bernd2704-cpu/bTn_Wecker/Hardware/Schaltplan/KiCad_Wecker_2v0/Wecker_2v0.kicad_sch

## KiCad design Hardware/Schaltplan/KiCad_Wecker_2v0/Wecker_2v0.kicad_sch (2026-10-06)

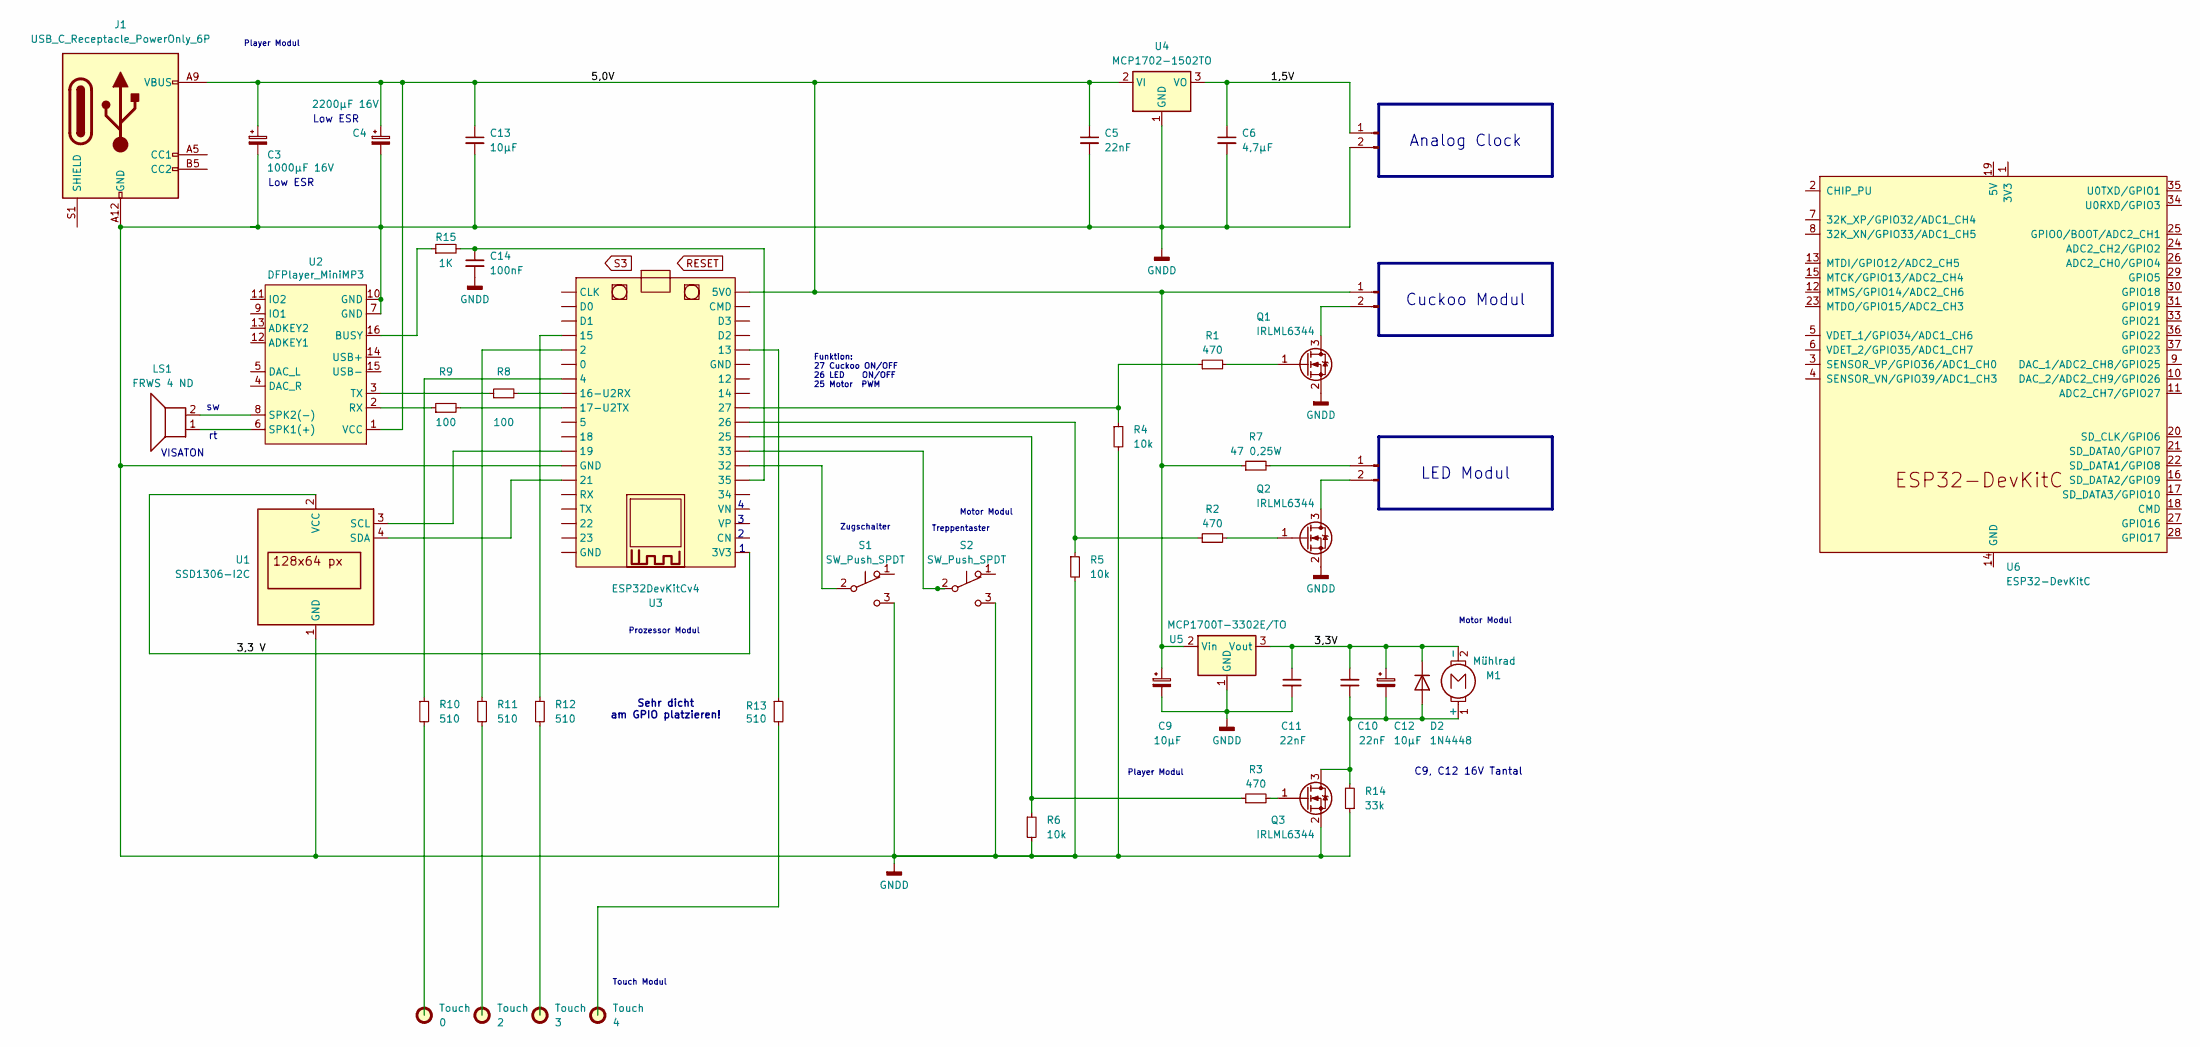
[picture p9: schematic Wecker_2v0.kicad_sch]

Parts:
C3: 1000µF 16V
C4: 2200µF 16V
C5, C10, C11: 22nF
C6: 4,7µF
C9, C12, C13: 10µF
C14: 100nF
D2: 1N4448; D_DO-41_SOD81_P10.16mm_Horizontal
J1: USB_C_Receptacle_PowerOnly_6P
J2, J3, J4: Conn_01x02_Pin
LS1: FRWS 4 ND
M1: Mühlrad
Q1, Q2, Q3: IRLML6344; SOT-23
R1, R2, R3: 470
R4, R5, R6: 10k
R7: 47 0,25W
R8, R9: 100
R10, R11, R12, R13: 510
R14: 33k
R15: 1K
S1, S2: SW_Push_SPDT
Touch: 4
U1: SSD1306-I2C; 0.96" SSD1306
U2: DFPlayer_MiniMP3
U3: ESP32DevKitCv4
U4: MCP1702-1502TO; SOT-223-3_TabPin2
U5: MCP1700T-3302E/TO; SOT-223-3_TabPin2
U6: ESP32-DevKitC

Connections:
1,5V: C6.1, J2.1, U4.3 (VO)
3,3 V: U1.2 (VCC), U3.20 (3V3)
3,3V: C10.1, C11.1, C12.1, D2.1 (K), M1.2 (-), U5.3 (Vout)
5,0V: C3.1, C4.1, C5.1, C9.1, C13.1, J1.A9 (VBUS), J1.B9 (VBUS), J3.1, R7.1, U2.1 (VCC), U3.38 (5V0), U4.2 (VI), U5.2 (Vin)
GNDD: C3.2, C4.2, C5.2, C6.2, C9.2, C11.2, C13.2, C14.2, J1.A12 (GND), J1.B12 (GND), J2.2, Q1.2 (S), Q2.2 (S), Q3.2 (S), R4.2, R5.2, R6.2, R14.1, S1.3 (C), S2.3 (C), U1.1 (GND), U2.7 (GND), U2.10 (GND), U3.13 (GND), U4.1 (GND), U5.1 (GND)
unnamed: C10.2, C12.2, D2.2 (A), M1.1 (+), Q3.3 (D), R14.2
unnamed: C14.1, R15.2, U3.25 (35)
unnamed: J3.2, Q1.3 (D)
unnamed: J4.1, R7.2
unnamed: J4.2, Q2.3 (D)
unnamed: LS1.1, U2.6 (SPK1(+))
unnamed: LS1.2, U2.8 (SPK2(-))
unnamed: Q1.1 (G), R1.2
unnamed: Q2.1 (G), R2.2
unnamed: Q3.1 (G), R3.2
unnamed: R1.1, R4.1, U3.30 (27)
unnamed: R2.1, R5.1, U3.29 (26)
unnamed: R3.1, R6.1, U3.28 (25)
unnamed: R8.1, U2.3 (TX)
unnamed: R8.2, U3.8 (16-U2RX)
unnamed: R9.1, U2.2 (RX)
unnamed: R9.2, U3.9 (17-U2TX)
unnamed: R10.1, U3.7 (4)
unnamed: R11.1, U3.5 (2)
unnamed: R12.1, U3.4 (15)
unnamed: R13.1, U3.34 (13)
unnamed: R15.1, U2.16 (BUSY)
unnamed: S1.2 (B), U3.26 (32)
unnamed: S2.2 (B), U3.27 (33)
unnamed: U1.3 (SCL), U3.12 (19)
unnamed: U1.4 (SDA), U3.14 (21)
unnamed: U6.14 (GND), U6.32 (GND), U6.38 (GND)

Notes on the sheet:
Sehr dicht am GPIO platzieren!
Player Modul
Prozessor Modul
Low ESR
Motor Modul
C9, C12 16V Tantal
Funktion: 27 Cuckoo ON/OFF 26 LED ON/OFF 25 Motor PWM
Treppentaster
VISATON
Touch Modul
Zugschalter
Analog Clock
LED Modul
Cuckoo Modul
